Freshynex/ProMicro-MidiController/_pics/CR/jpg/carrier/cb_layoutcheck2.jpg

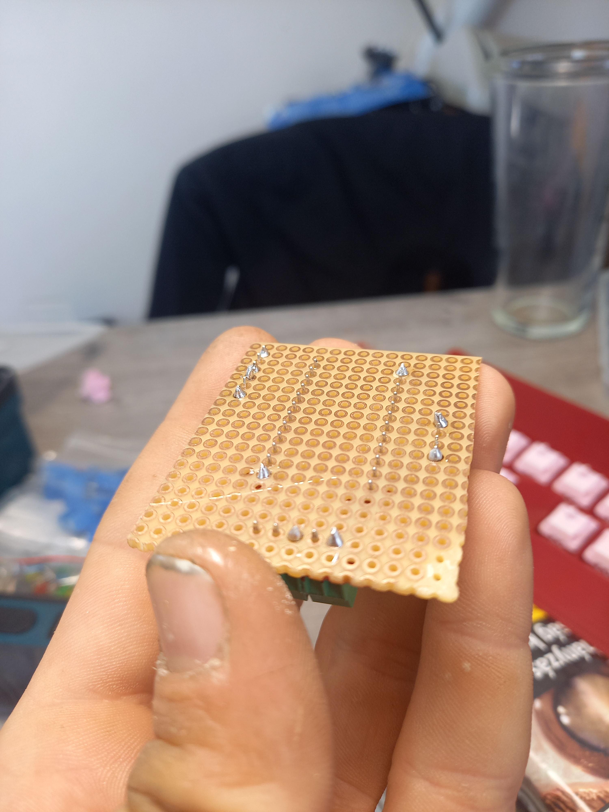
_pics/CR/jpg/carrier/cb_layoutcheck2.jpg
