Freshynex/ProMicro-MidiController/_pics/CR/jpg/carrier/cb_pinconnection1.jpg

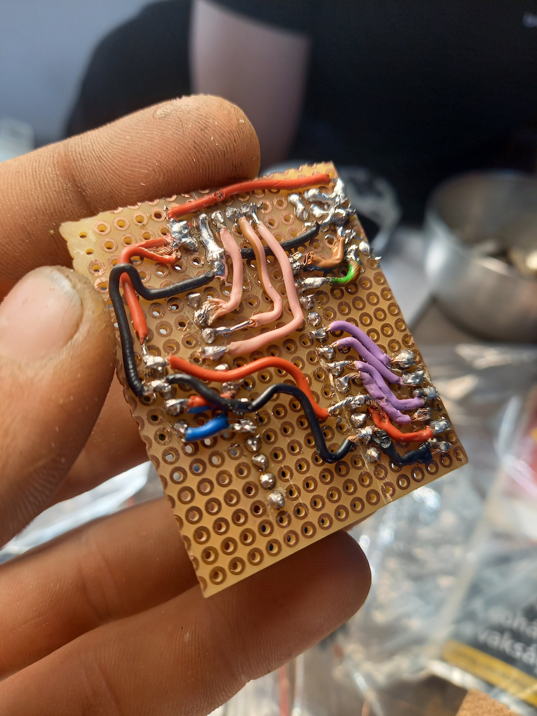
_pics/CR/jpg/carrier/cb_pinconnection1.jpg
