Freshynex/ProMicro-MidiController/_pics/CR/jpg/carrier/cb_pinconnection2.jpg

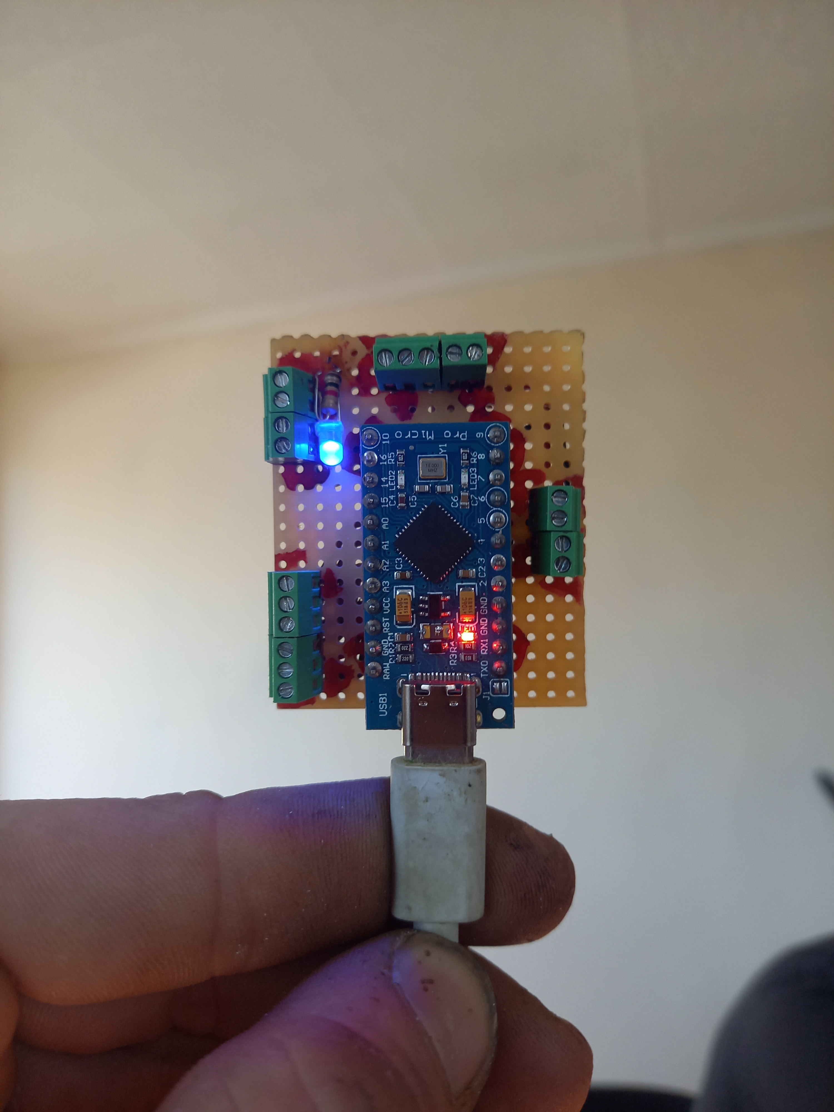
_pics/CR/jpg/carrier/cb_pinconnection2.jpg
