Freshynex/ProMicro-MidiController/_pics/CR/jpg/modules/analog/0_anal_module_rotconnection1.jpg

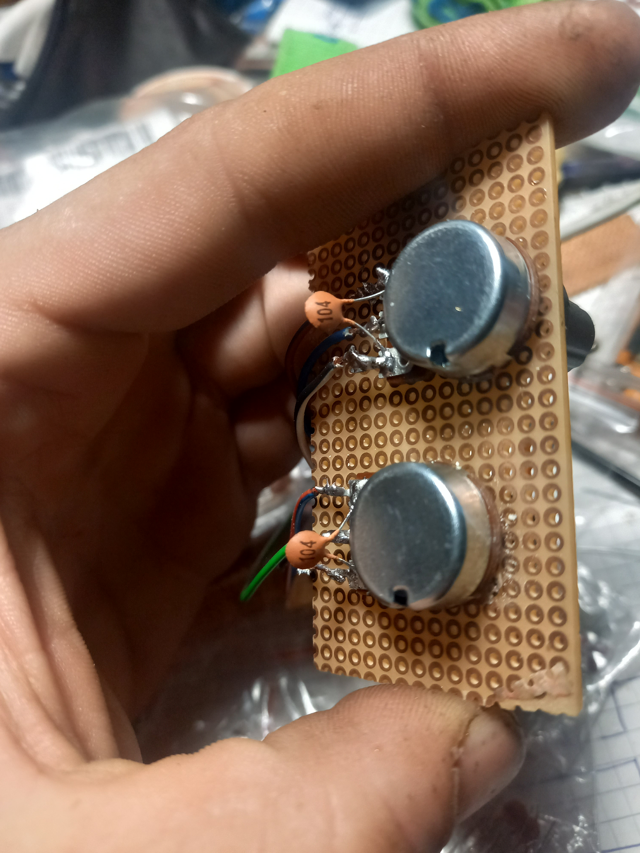
_pics/CR/jpg/modules/analog/0_anal_module_rotconnection1.jpg
