Freshynex/ProMicro-MidiController/_pics/CR/jpg/modules/keyboard/0_kb_module_layouttest3.jpg

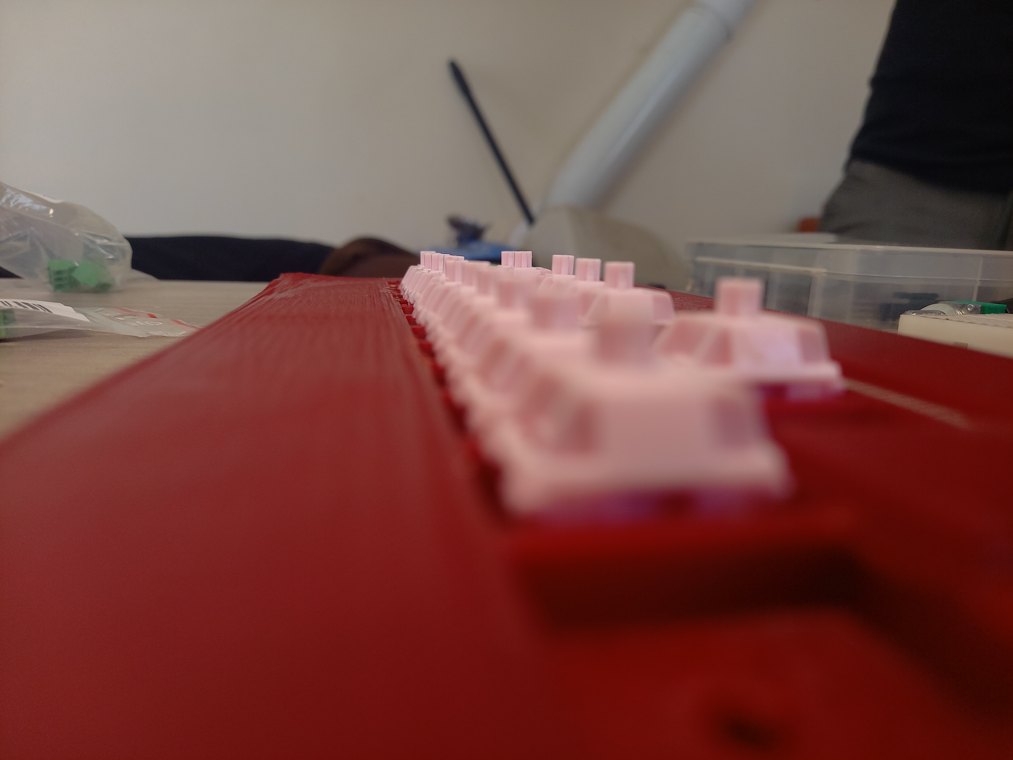
_pics/CR/jpg/modules/keyboard/0_kb_module_layouttest3.jpg
