Freshynex/ProMicro-MidiController/_pics/CR/jpg/modules/keyboard/1_kb_module_layout3.jpg

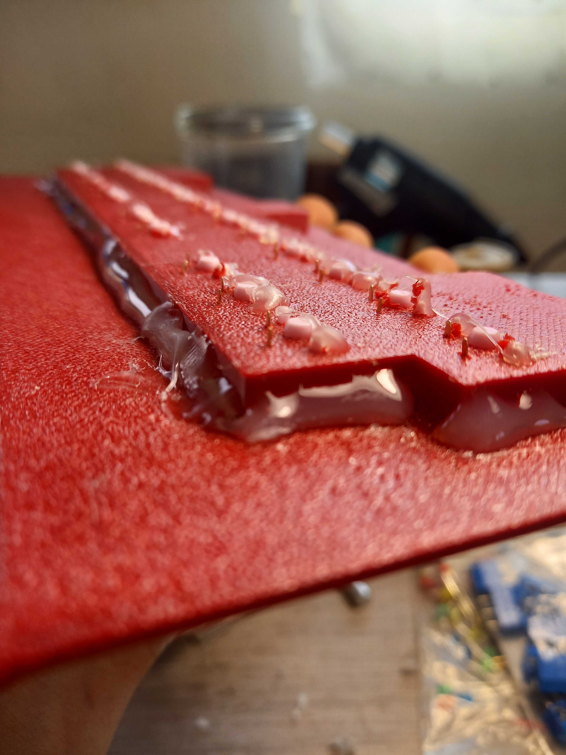
_pics/CR/jpg/modules/keyboard/1_kb_module_layout3.jpg
