Freshynex/ProMicro-MidiController/_pics/CR/jpg/modules/keyboard/2_kb_module_comconnection2.jpg

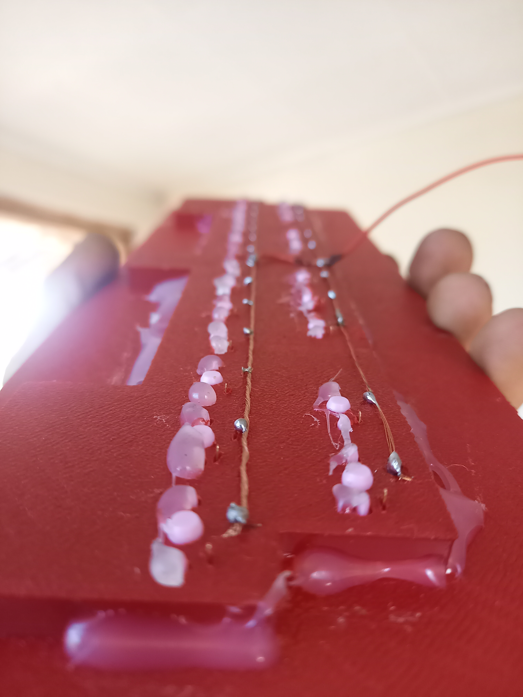
_pics/CR/jpg/modules/keyboard/2_kb_module_comconnection2.jpg
