Freshynex/ProMicro-MidiController/_pics/CR/jpg/modules/keyboard/3_kb_module_registerlayout.jpg

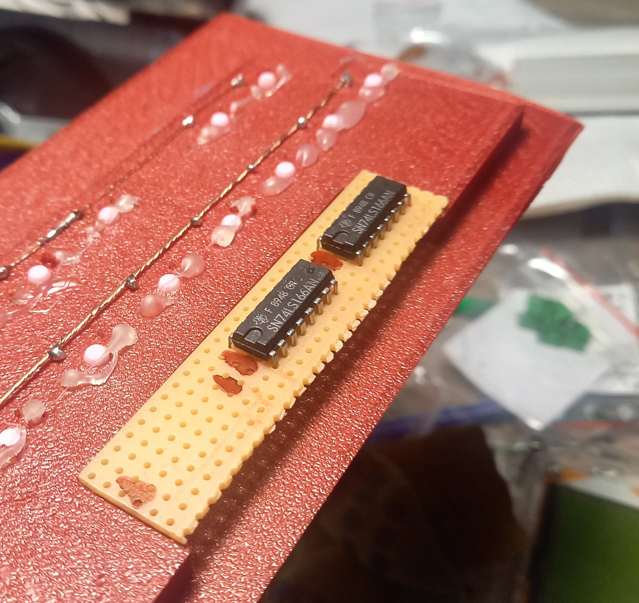
_pics/CR/jpg/modules/keyboard/3_kb_module_registerlayout.jpg
