Freshynex/ProMicro-MidiController/schematic & pcb/exports/anal_3d_1.jpg

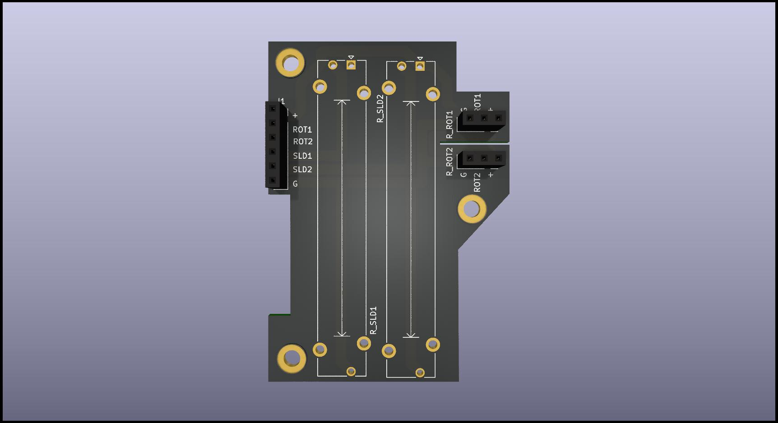
schematic & pcb/exports/anal_3d_1.jpg
