Freshynex/ProMicro-MidiController/schematic & pcb/exports/anal_3d_3.jpg

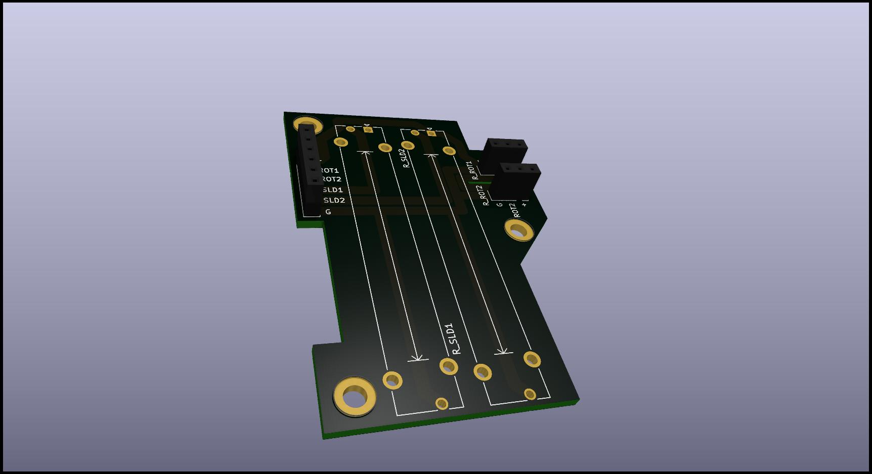
schematic & pcb/exports/anal_3d_3.jpg
