Freshynex/ProMicro-MidiController/schematic & pcb/exports/carrier_3d_1.jpeg

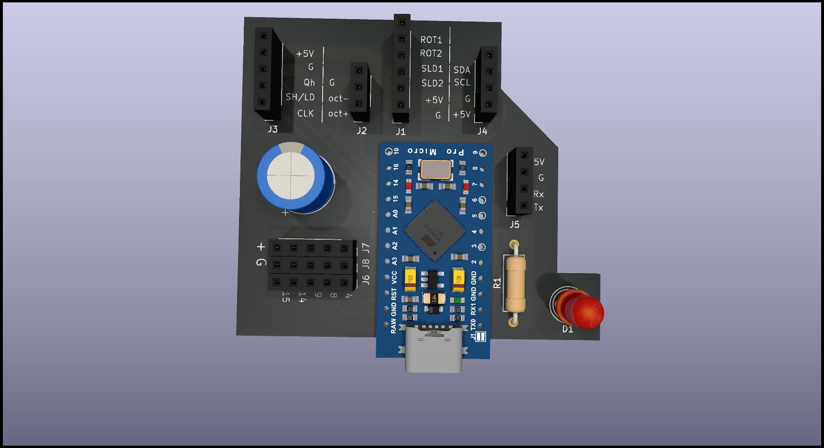
schematic & pcb/exports/carrier_3d_1.jpeg
