Freshynex/ProMicro-MidiController/schematic & pcb/exports/carrier_3d_3.jpeg

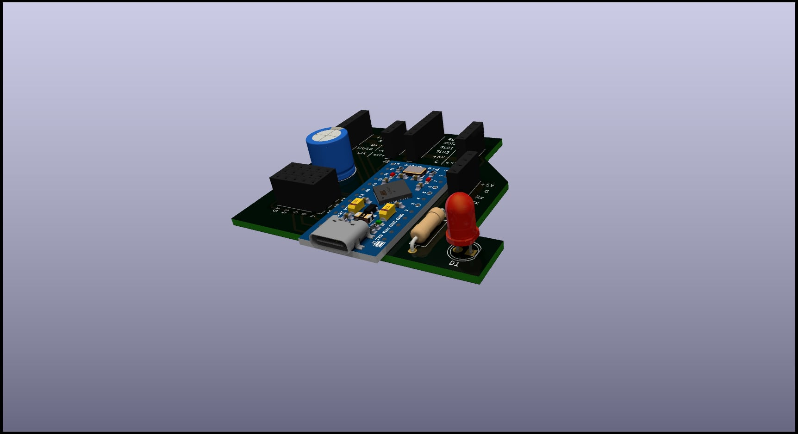
schematic & pcb/exports/carrier_3d_3.jpeg
