Freshynex/ProMicro-MidiController/schematic & pcb/exports/kb_3d_1.jpeg

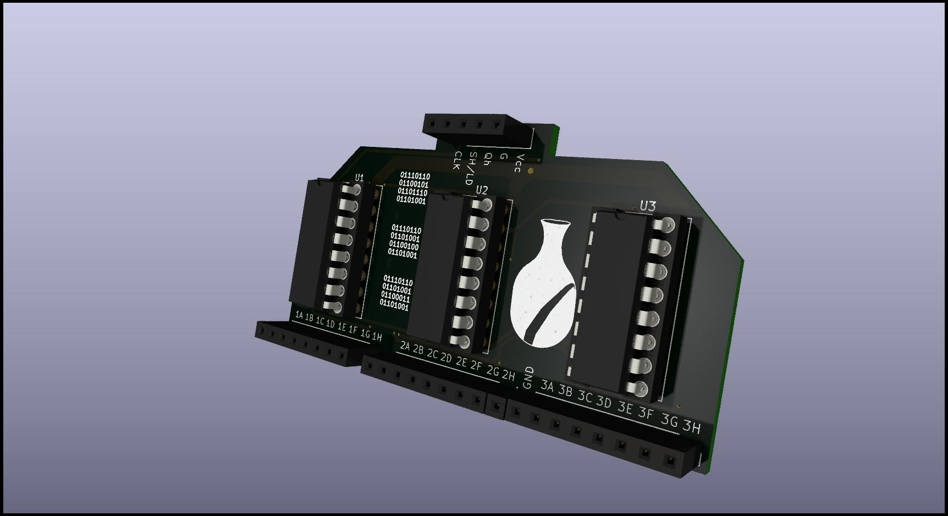
schematic & pcb/exports/kb_3d_1.jpeg
