Freshynex/ProMicro-MidiController/schematic & pcb/exports/kb_3d_2.jpeg

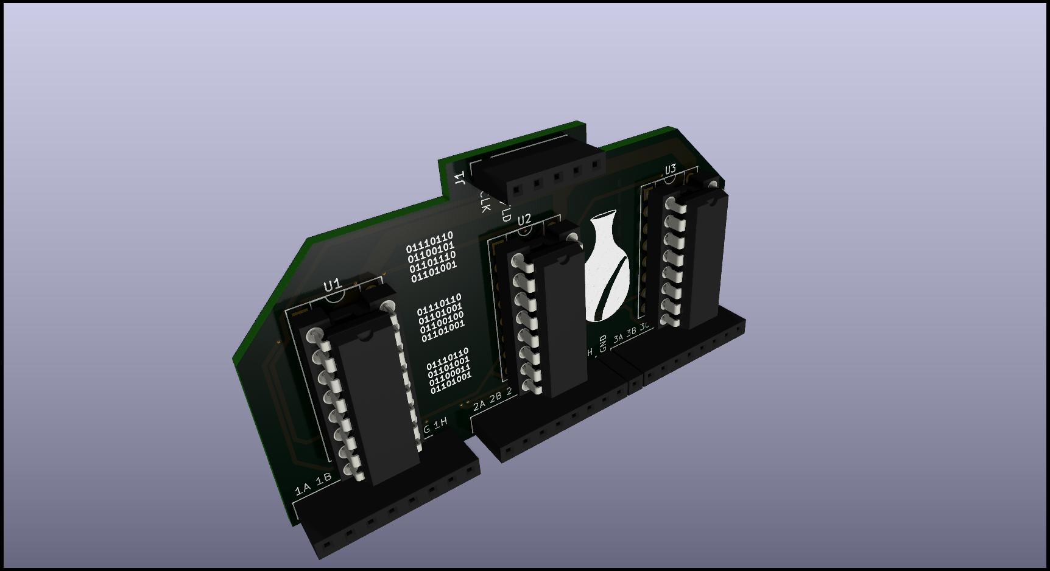
schematic & pcb/exports/kb_3d_2.jpeg
