Freshynex/ProMicro-MidiController/schematic & pcb/exports/octstp_3d_1.jpg

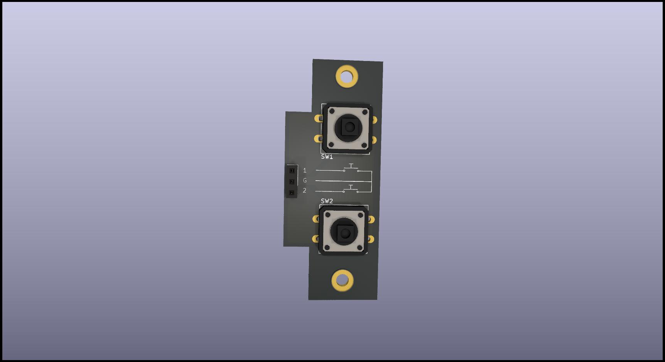
schematic & pcb/exports/octstp_3d_1.jpg
