Freshynex/ProMicro-MidiController/schematic & pcb/exports/octstp_3d_3.jpg

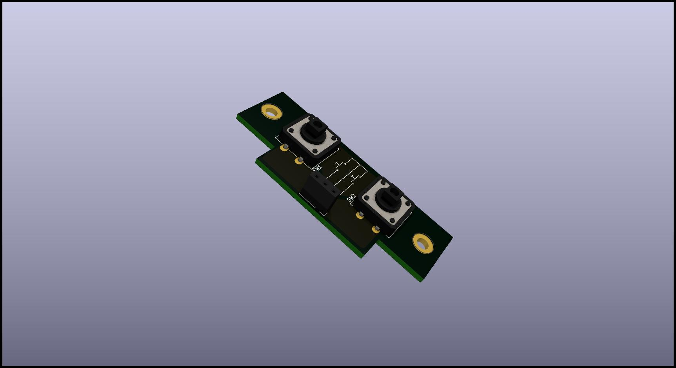
schematic & pcb/exports/octstp_3d_3.jpg
