Freshynex/ProMicro-MidiController/_pics/CR/jpg/modules/octave_step/0_octstep_module_layoutconnection2.jpg

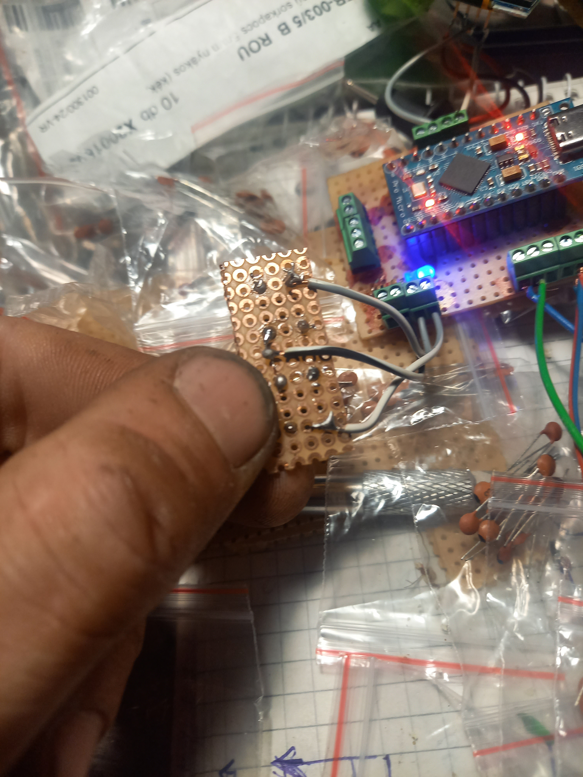
_pics/CR/jpg/modules/octave_step/0_octstep_module_layoutconnection2.jpg
