Freshynex/ProMicro-MidiController/_pics/CR/gif/i2c_dsply_test_cube.gif

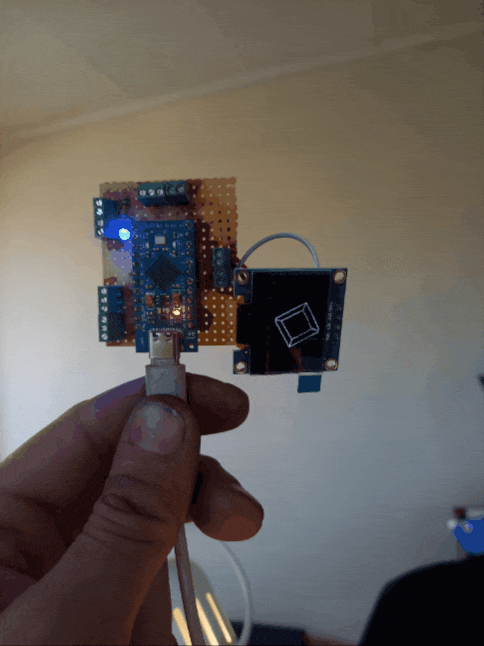
_pics/CR/gif/i2c_dsply_test_cube.gif
